Vail-CW/vail-adapter/online-updater/images/1.jpg

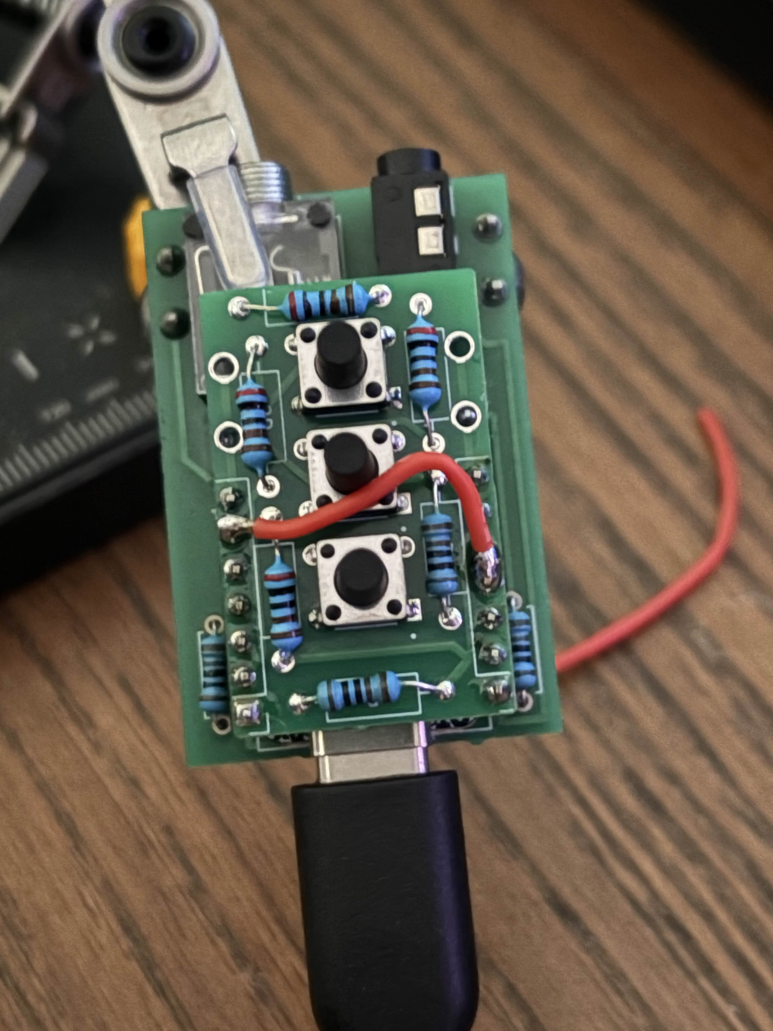
online-updater/images/1.jpg
