Vail-CW/vail-adapter/online-updater/images/2.jpg

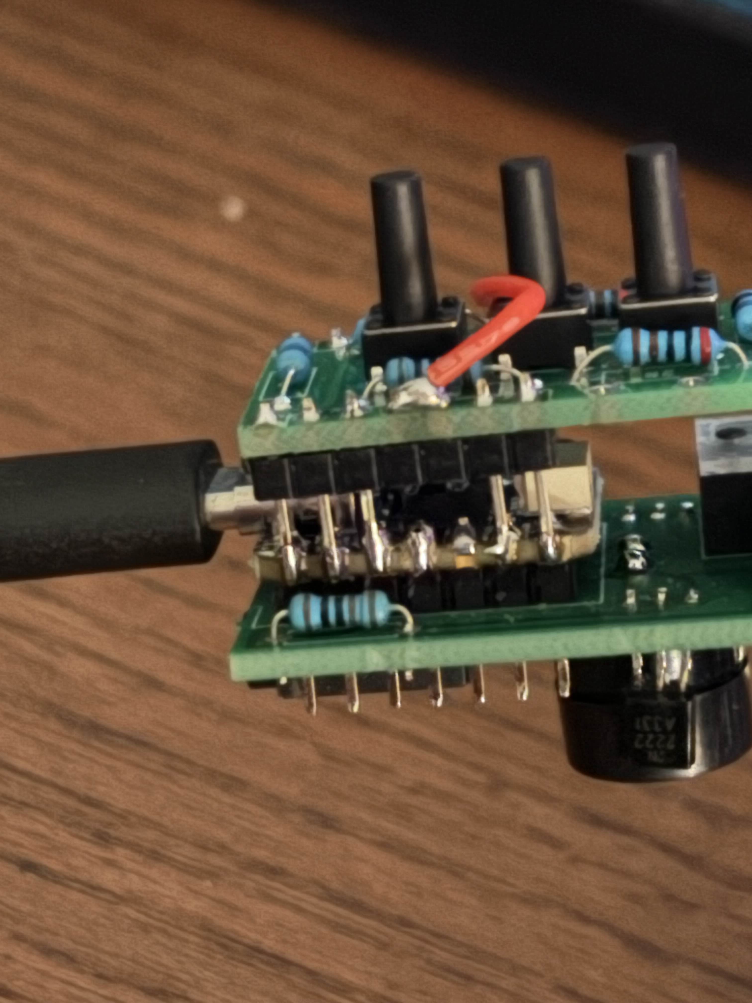
online-updater/images/2.jpg
