Vail-CW/vail-adapter/equal_temperament.cpp

#include "equal_temperament.h"

const uint16_t equalTemperamentNote[128] PROGMEM = {
    8, 8, 9, 9, 10, 10, 11, 12, 12, 13, 14, 15, 16, 17, 18, 19,
    20, 21, 23, 24, 25, 27, 29, 30, 32, 34, 36, 38, 41, 43, 46, 49,
    51, 55, 58, 61, 65, 69, 73, 77, 82, 87, 92, 98, 103, 110, 116, 123,
    130, 138, 146, 155, 164, 174, 185, 196, 207, 220, 233, 247, 261, 277, 293, 311,
    329, 349, 370, 392, 415, 440, 466, 494, 523, 554, 587, 622, 659, 698, 740, 784,
    831, 880, 932, 988, 1047, 1109, 1175, 1245, 1319, 1397, 1480, 1568, 1662, 1760, 1865, 1976,
    2094, 2218, 2350, 2490, 2638, 2795, 2961, 3137, 3324, 3521, 3731, 3953, 4188, 4437, 4701, 4980,
    5276, 5590, 5922, 6275, 6648, 7043, 7462, 7906, 8376, 8874, 9402, 9961, 10553, 11181, 11845, 12550
};
