Vail-CW/vail-adapter/polybuzzer.h

#pragma once

#include <Arduino.h>

// On memory-constrained AVR boards (e.g. Arduino Micro / ATmega32U4)
// drop to a single tone slot to save SRAM. SAMD21 keeps 2 slots for
// the priority overlay behavior used by DisableBuzzer / Morse playback.
#if defined(__AVR__)
  #define POLYBUZZER_MAX_TONES 1
#else
  #define POLYBUZZER_MAX_TONES 2
#endif

// PolyBuzzer provides a proritized monophonic buzzer.
//
// A given tone will only be played when all higher priority tones have stopped.
class PolyBuzzer {
public:
    unsigned int tones[POLYBUZZER_MAX_TONES];
    unsigned int playing;
    uint8_t pin;

    PolyBuzzer(uint8_t pin);
    void update();
    void Tone(int slot, unsigned int frequency);
    void Note(int slot, uint8_t note);
    void NoTone(int slot);
    
    // Debug helper - print current state
    void printDebugInfo() {
        Serial.print("PolyBuzzer - Current tones: [");
        for (int i = 0; i < POLYBUZZER_MAX_TONES; i++) {
            Serial.print(tones[i]);
            if (i < POLYBUZZER_MAX_TONES - 1) Serial.print(", ");
        }
        Serial.print("], Playing: ");
        Serial.println(playing);
    }
};
